decuatroide/FUNBIOB402/Talleres2/Bridgitte Pomachagua/brigitte pomachagua.pdf

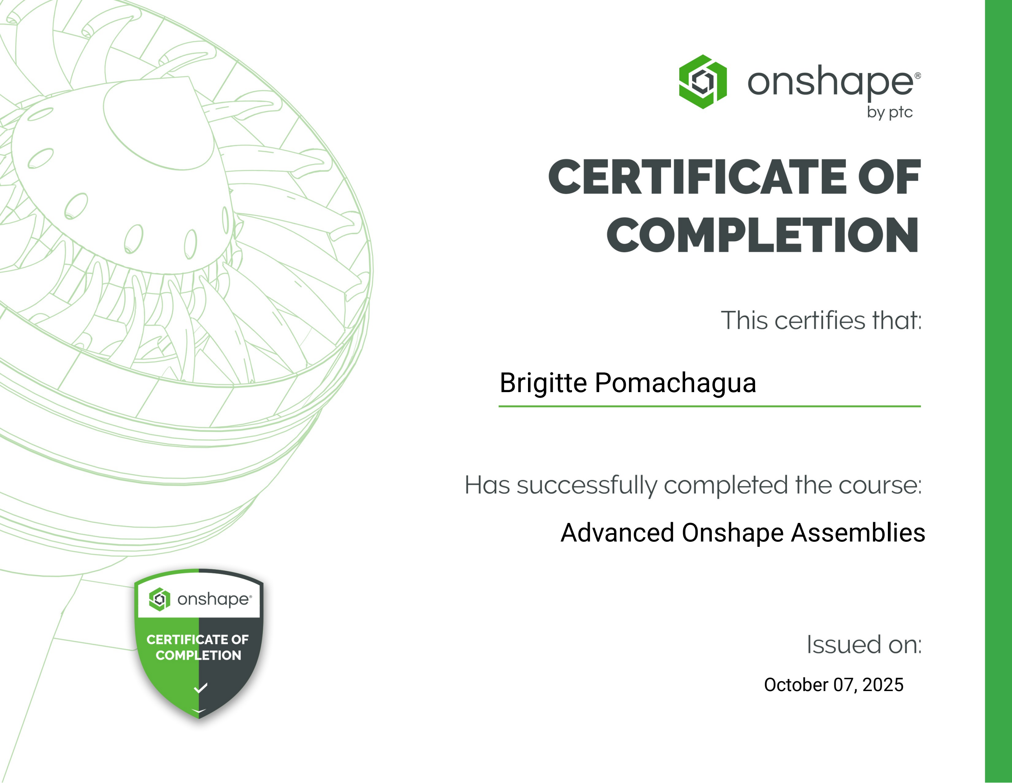
[picture p50: page 1]

Brigitte Pomachagua

Advanced Onshape Assemblies

October 07, 2025
