decuatroide/FUNBIOB402/Talleres2/Leonardo/certificado_taller_elementos_mecánicos Leonardo.pdf

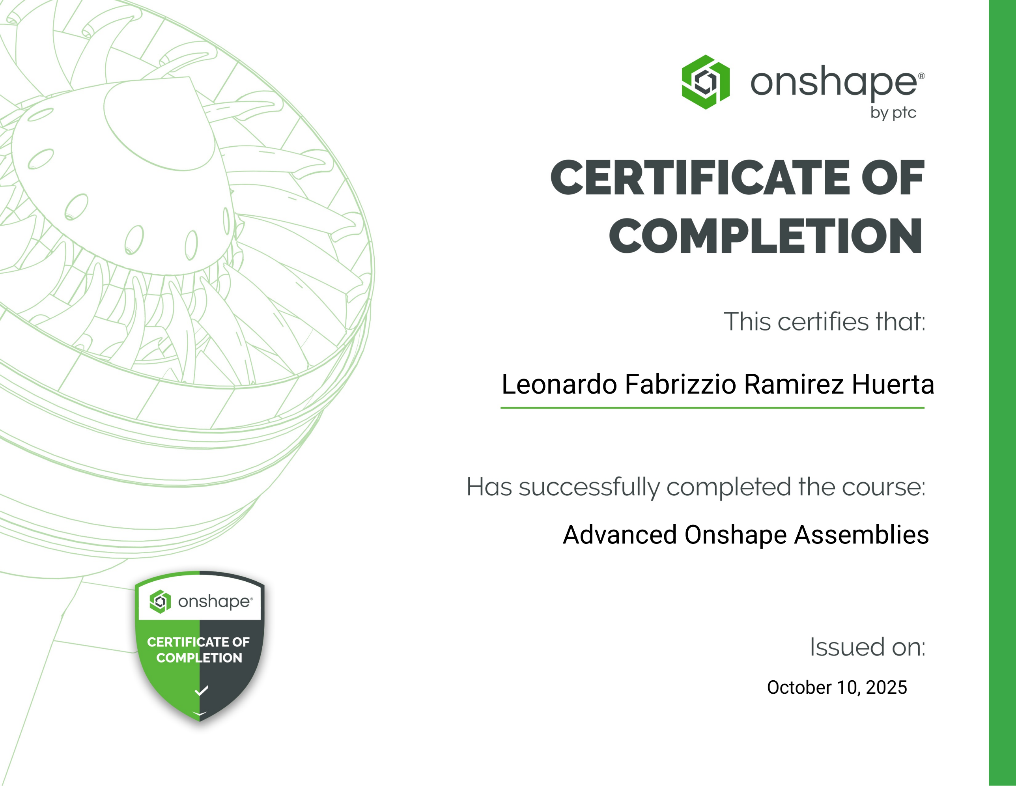
[picture p51: page 1]

Leonardo Fabrizzio Ramirez Huerta

Advanced Onshape Assemblies

October 10, 2025
