decuatroide/FUNBIOB402/Talleres2/Marcela Rojas/certificado taller elementos mecánicos marcela.pdf

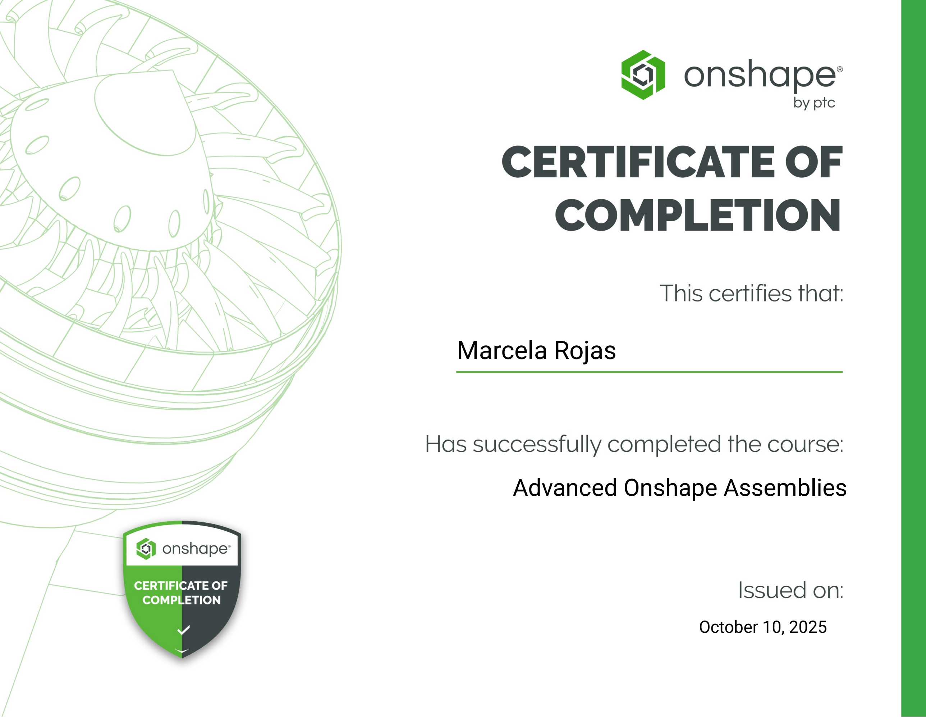
[picture p52: page 1]

Marcela Rojas

Advanced Onshape Assemblies

October 10, 2025
