decuatroide/FUNBIOB402/Talleres2/Oliver/oliver-rimapa-26de84b9-6e77-49f1-8246-cdd332178522-certificate.pdf

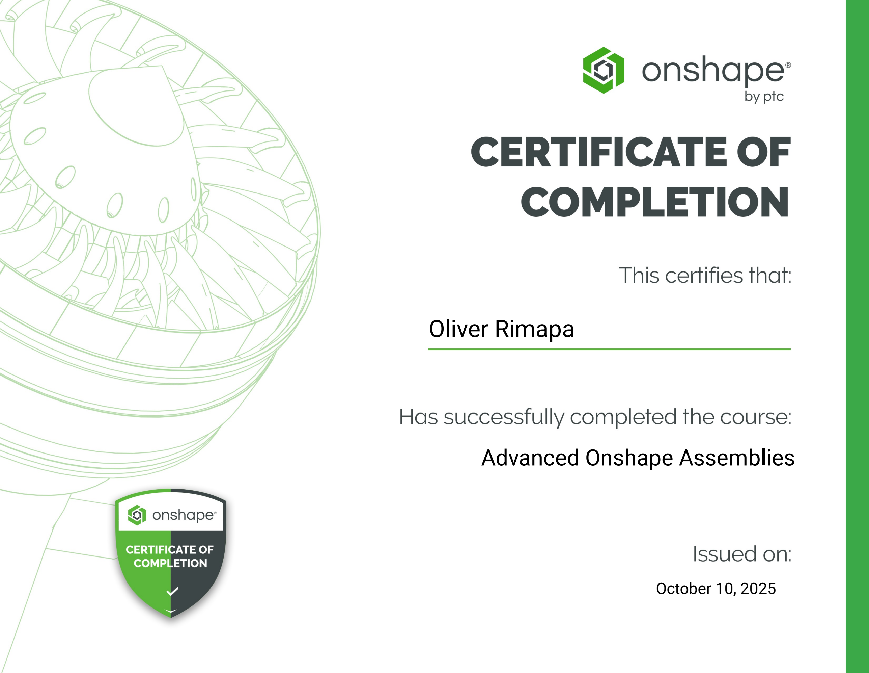
[picture p53: page 1]

Oliver Rimapa

Advanced Onshape Assemblies

October 10, 2025
