decuatroide/FUNBIOB402/Talleres/Briggite/Brigitte Pomachagua.pdf

Brigitte Pomachagua

Introduction to Sketching

September 17, 2025

Brigitte Pomachagua

Introduction to Part Studios

September 19, 2025

Brigitte Pomachagua

September 19, 2025

Multi-Part Part Studios

Brigitte Pomachagua

September 19, 2025

Onshape Assemblies

Brigitte Pomachagua

September 19, 2025

Detailed Drawings
