decuatroide/FUNBIOB402/Talleres/Leonardo/leonardo-fabrizzio-ramirez-huerta-00f52e10-80f0-4916-abce-2b37d8ef5526-certificate.pdf

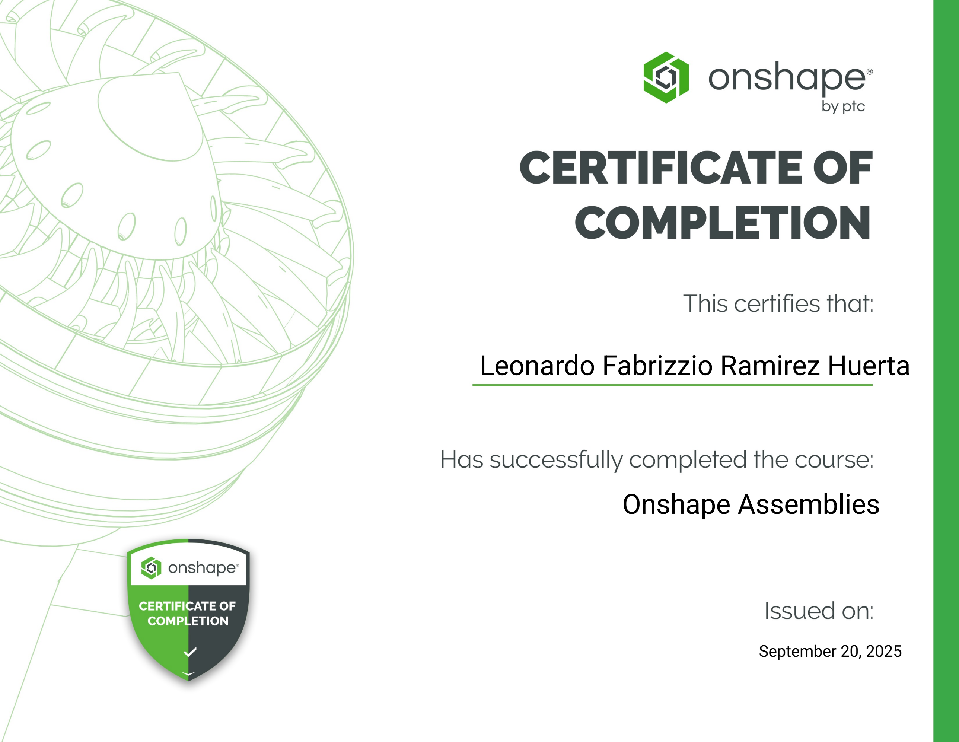
[picture p54: page 1]

Leonardo Fabrizzio Ramirez Huerta

September 20, 2025

Onshape Assemblies
