decuatroide/FUNBIOB402/Talleres/Oliver/oliver-rimapa-e7845775-140b-470d-8c00-d0a61c5a247d-certificate.pdf

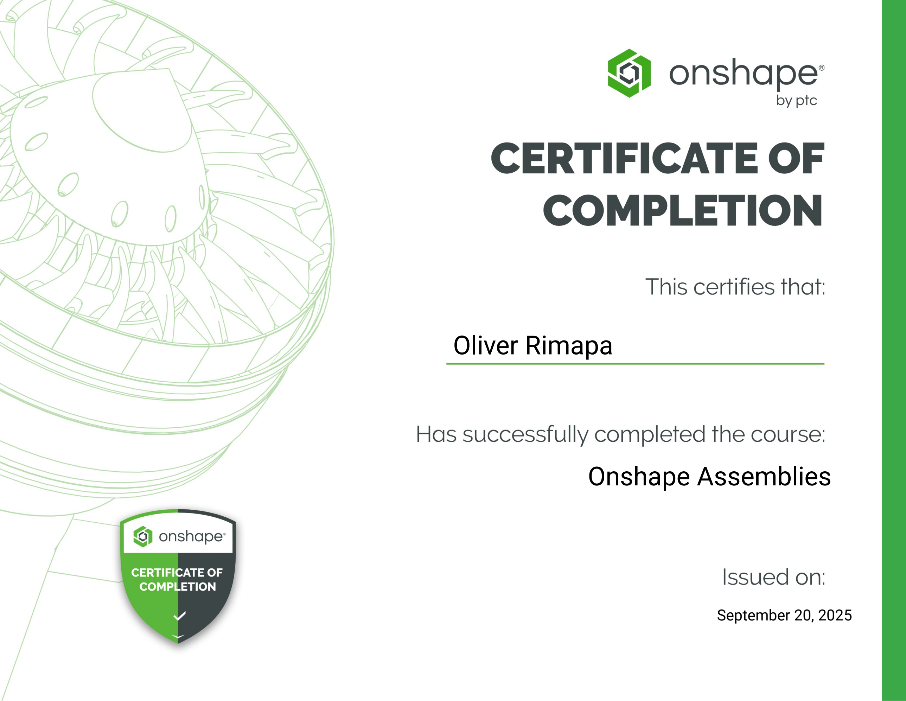
[picture p55: page 1]

Oliver Rimapa

September 20, 2025

Onshape Assemblies
