decuatroide/FUNBIOB402/Talleres/Marcela/certificado 5.pdf

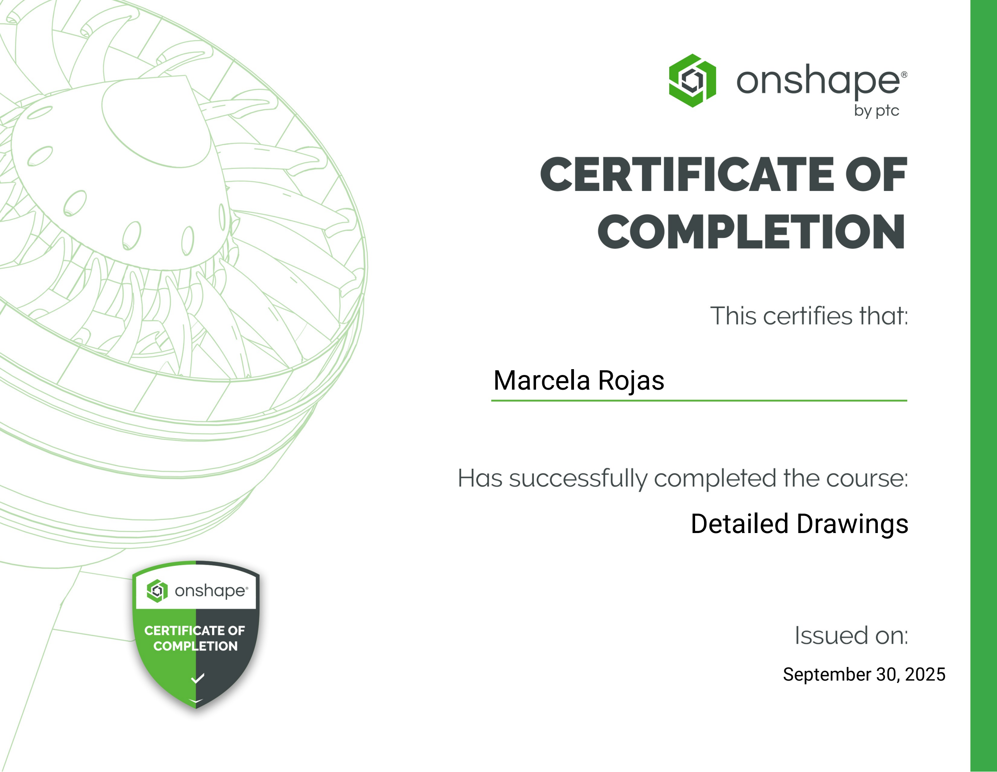
[picture p73: page 1]

Marcela Rojas

September 30, 2025

Detailed Drawings
