decuatroide/FUNBIOB402/Talleres/Marcela/certificado 3.pdf

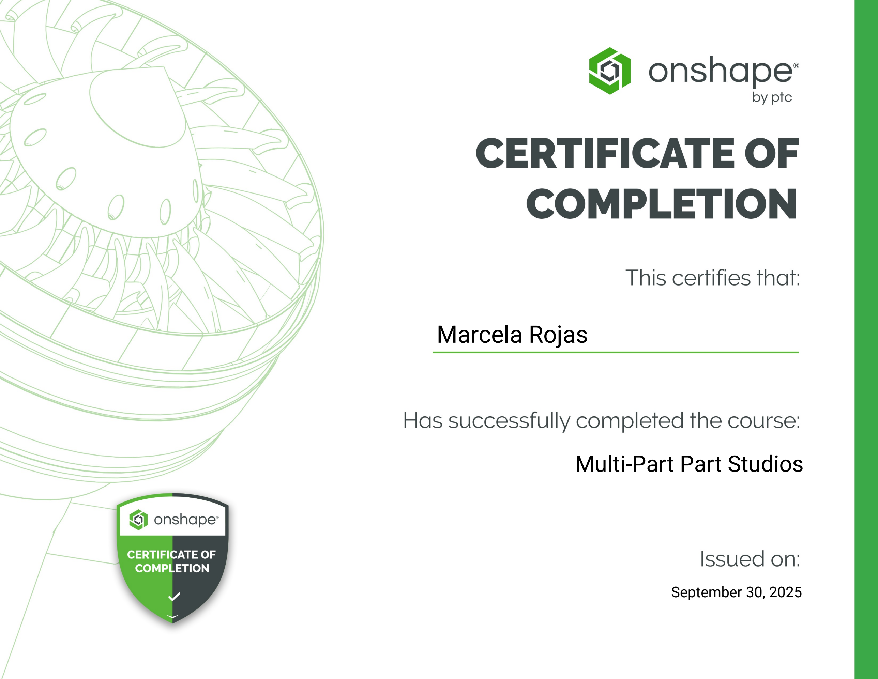
[picture p74: page 1]

Marcela Rojas

September 30, 2025

Multi-Part Part Studios
