decuatroide/FUNBIOB402/Talleres/Marcela/certificado 2.pdf

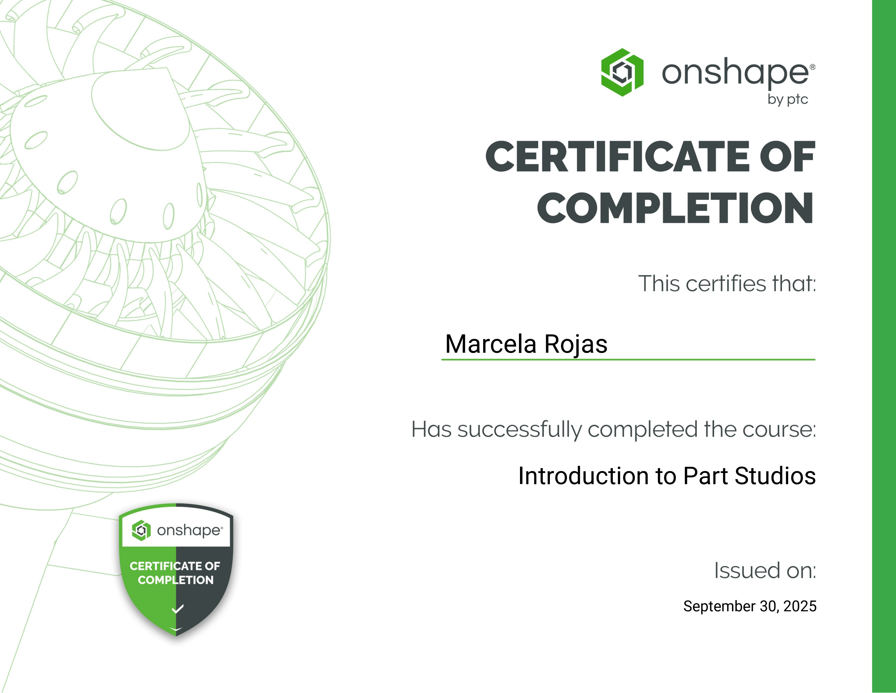
[picture p75: page 1]

Marcela Rojas

Introduction to Part Studios

September 30, 2025
