decuatroide/FUNBIOB402/Talleres/Marcela/certificado 1.pdf

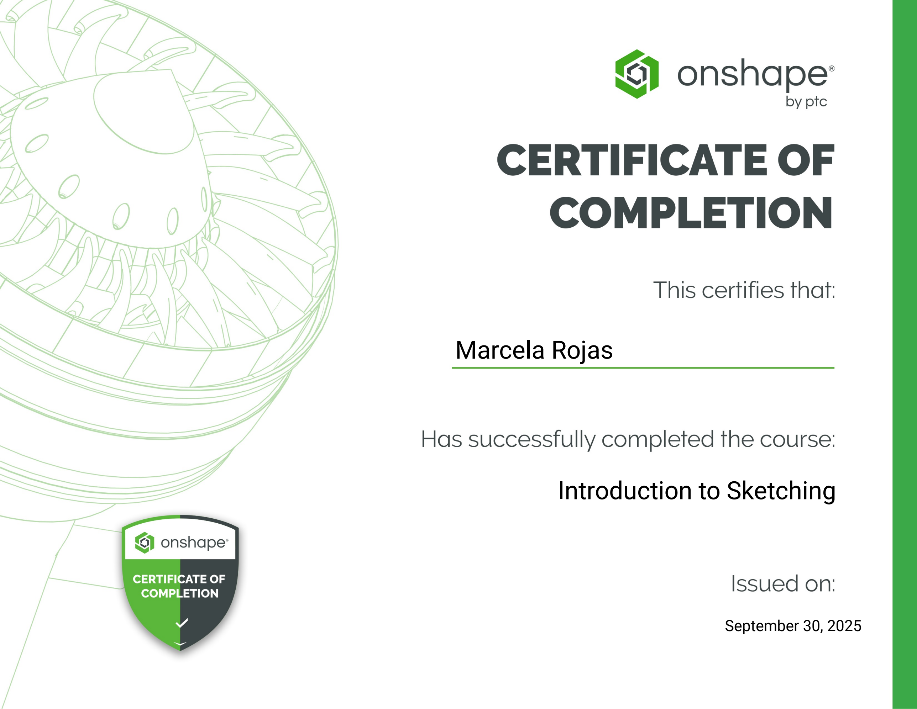
[picture p76: page 1]

Marcela Rojas

Introduction to Sketching

September 30, 2025
