decuatroide/FUNBIOB402/Talleres/Gabriel/Detailed Drawings.pdf

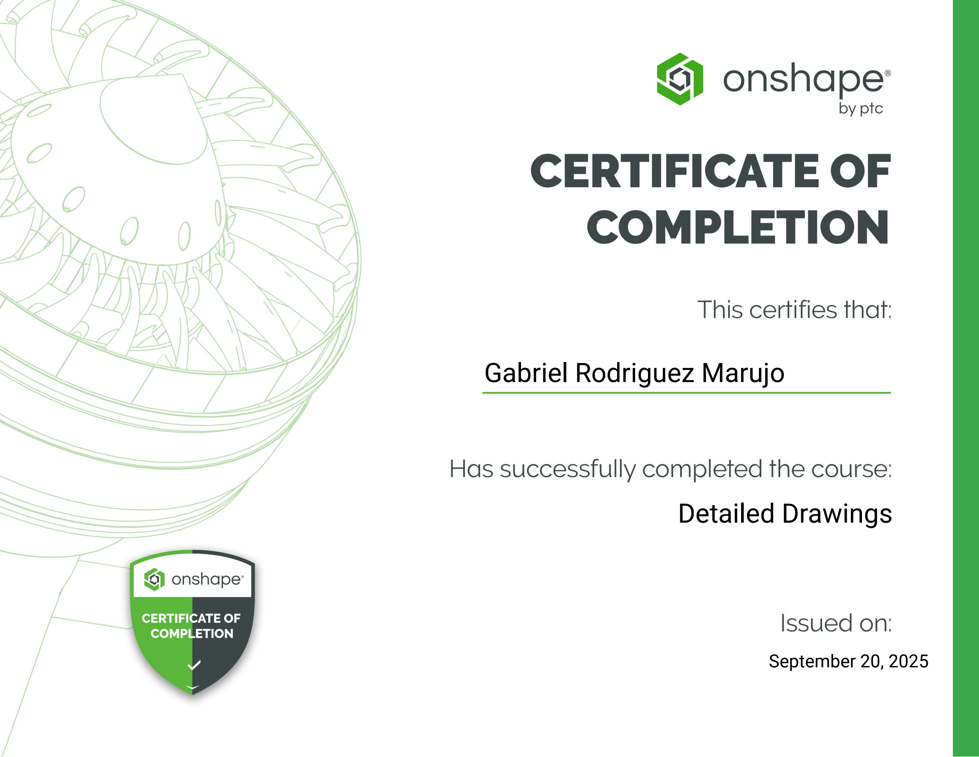
[picture p77: page 1]

Gabriel Rodriguez Marujo

September 20, 2025

Detailed Drawings
