decuatroide/FUNBIOB402/Talleres/Gabriel/Introduction to Part Studios.pdf

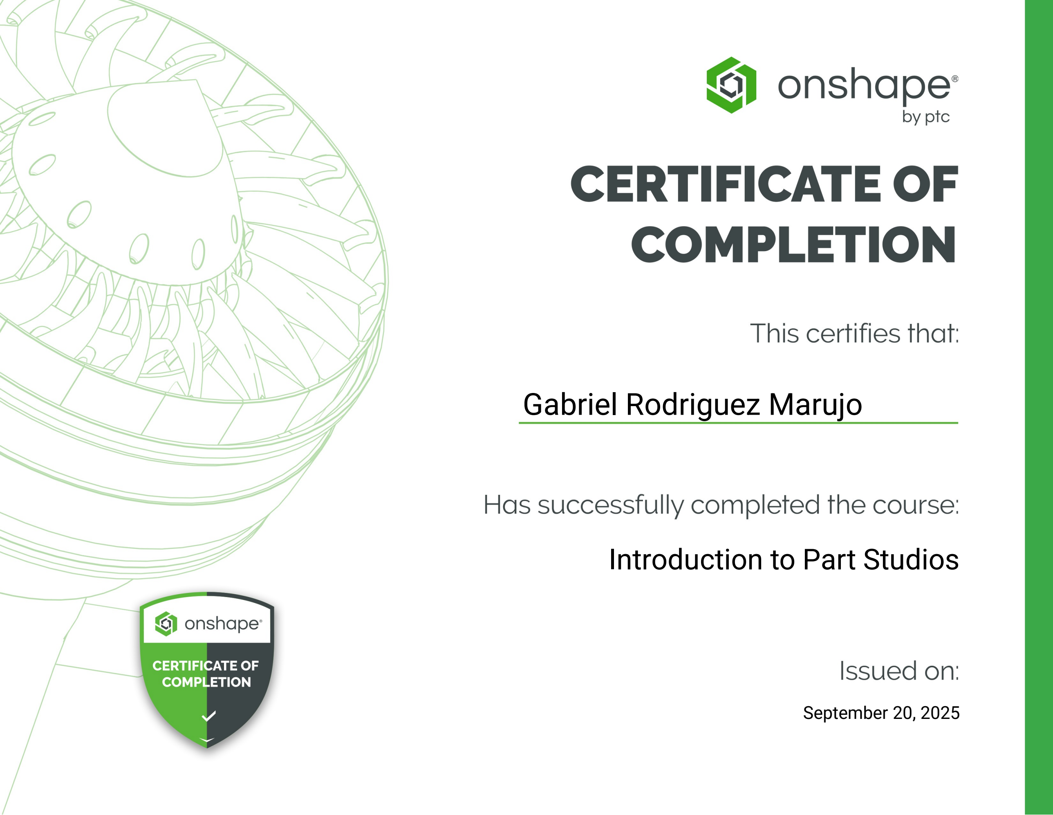
[picture p78: page 1]

Gabriel Rodriguez Marujo

Introduction to Part Studios

September 20, 2025
