decuatroide/FUNBIOB402/Talleres/Gabriel/Introduction to Sketching.pdf

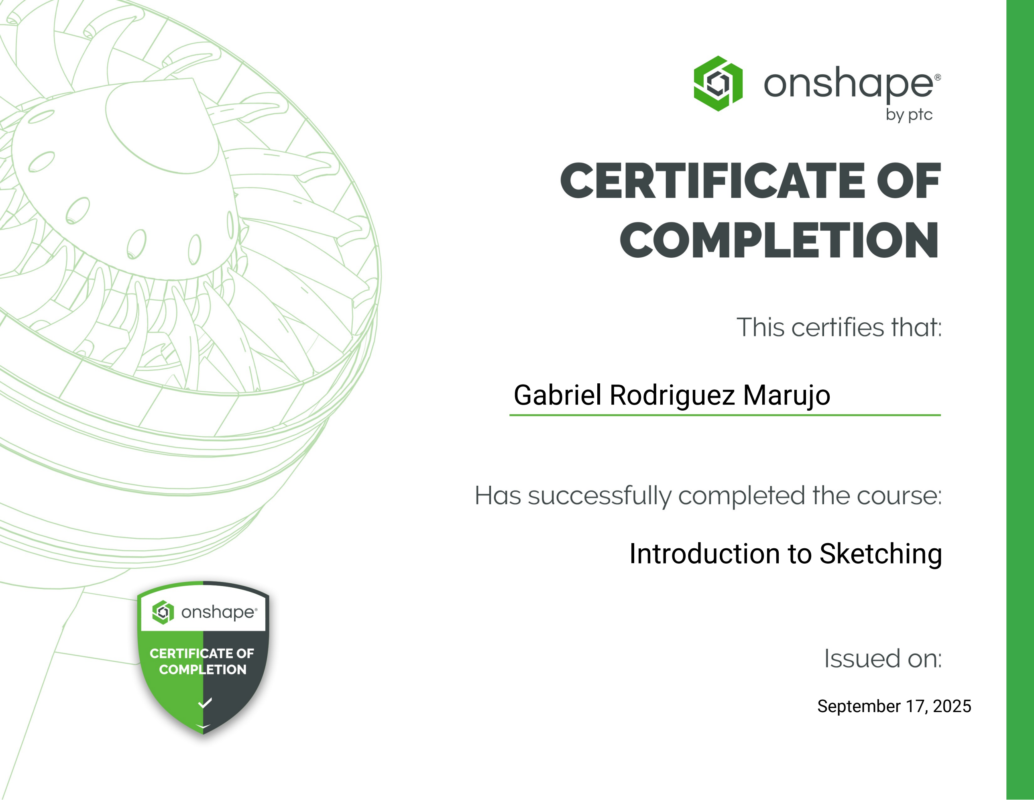
[picture p79: page 1]

Gabriel Rodriguez Marujo

Introduction to Sketching

September 17, 2025
