decuatroide/FUNBIOB402/Talleres/Gabriel/Multi-Part Part Studios.pdf

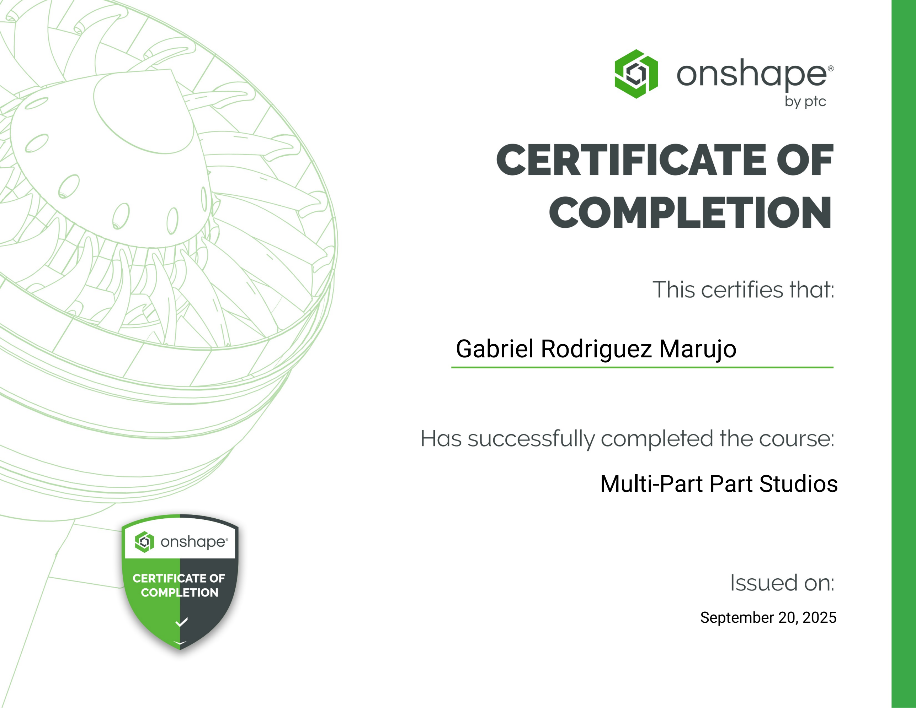
[picture p80: page 1]

Gabriel Rodriguez Marujo

September 20, 2025

Multi-Part Part Studios
