decuatroide/FUNBIOB402/Talleres/Leonardo/leonardo-fabrizzio-ramirez-huerta-042929c8-985e-4253-a575-43340ca856d0-certificate.pdf

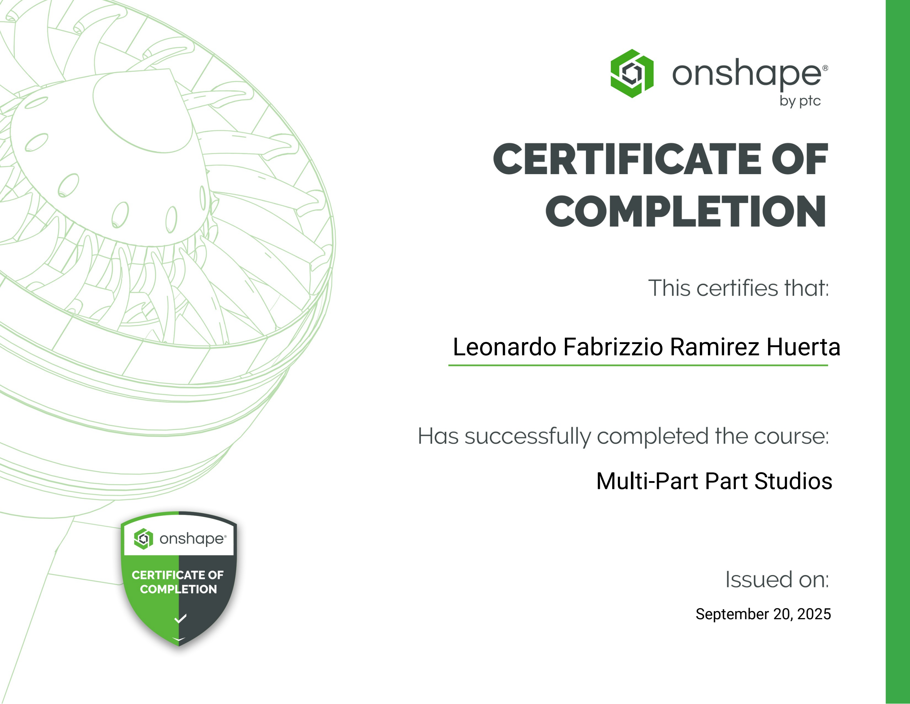
[picture p81: page 1]

Leonardo Fabrizzio Ramirez Huerta

September 20, 2025

Multi-Part Part Studios
