decuatroide/FUNBIOB402/Talleres/Leonardo/leonardo-fabrizzio-ramirez-huerta-1ade5dff-bad6-4393-ad0c-2083a6c78db8-certificate.pdf

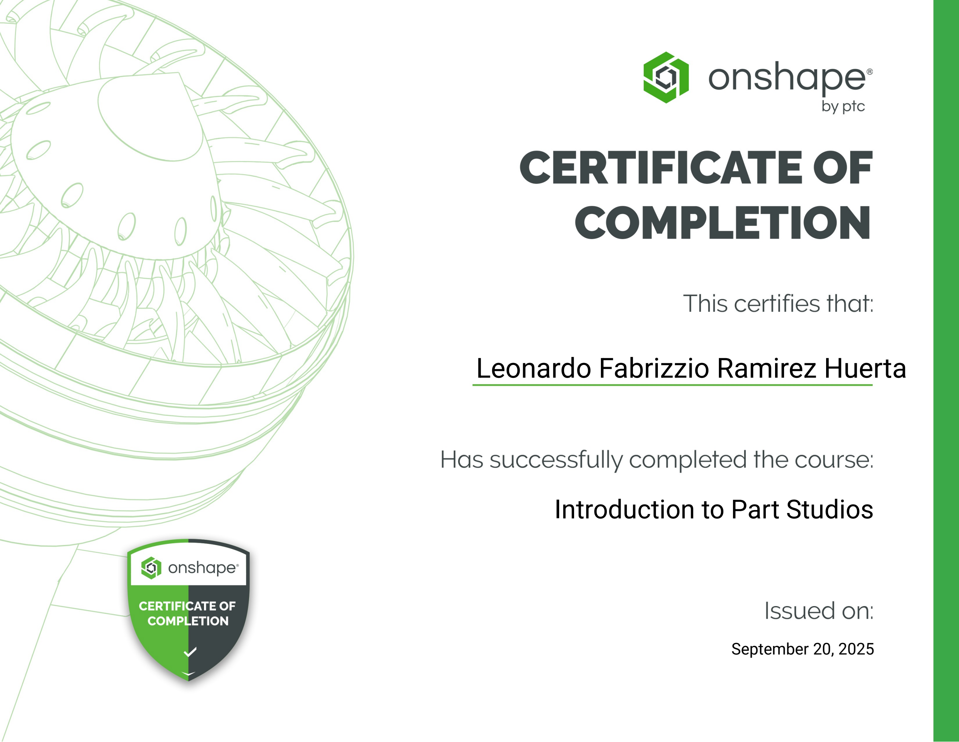
[picture p82: page 1]

Leonardo Fabrizzio Ramirez Huerta

Introduction to Part Studios

September 20, 2025
