decuatroide/FUNBIOB402/Talleres/Leonardo/leonardo-fabrizzio-ramirez-huerta-2d4dcfee-9d83-4cb5-a097-950389071dda-certificate.pdf

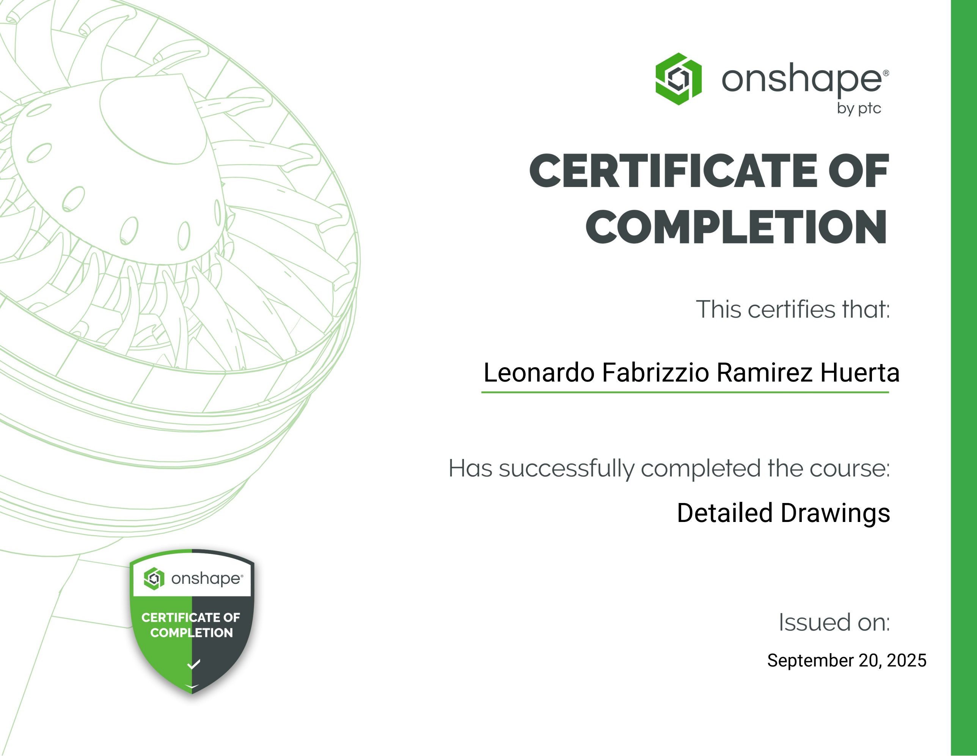
[picture p83: page 1]

Leonardo Fabrizzio Ramirez Huerta

September 20, 2025

Detailed Drawings
