decuatroide/FUNBIOB402/Talleres/Leonardo/leonardo-fabrizzio-ramirez-huerta-379ba665-cea7-4060-8885-238d04ed1d95-certificate.pdf

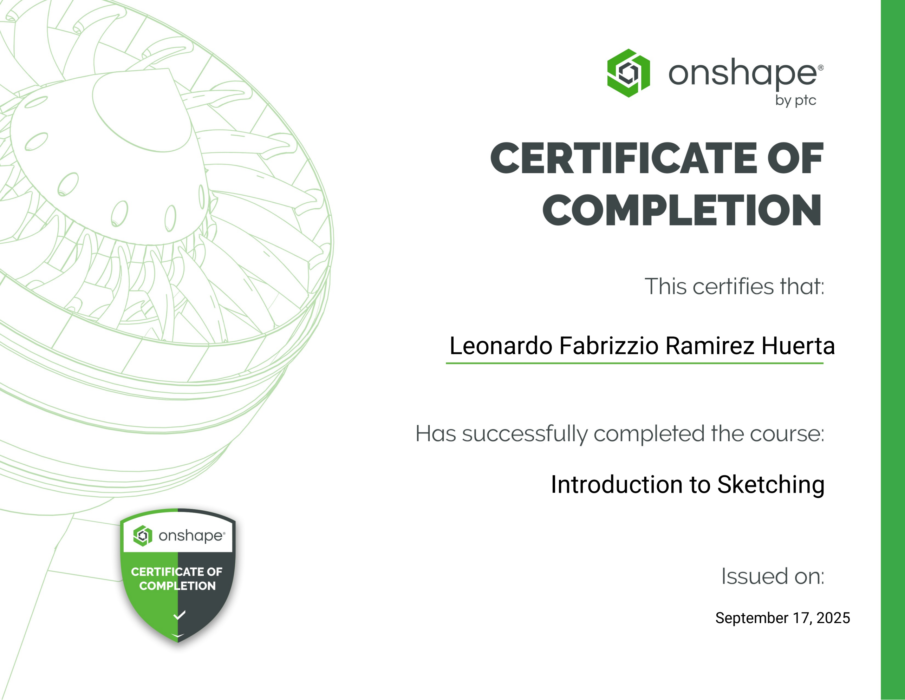
[picture p84: page 1]

Leonardo Fabrizzio Ramirez Huerta

Introduction to Sketching

September 17, 2025
