decuatroide/FUNBIOB402/Talleres/Oliver/oliver-rimapa-0e1e60df-f512-4e64-acf3-dd76d66e0818-certificate.pdf

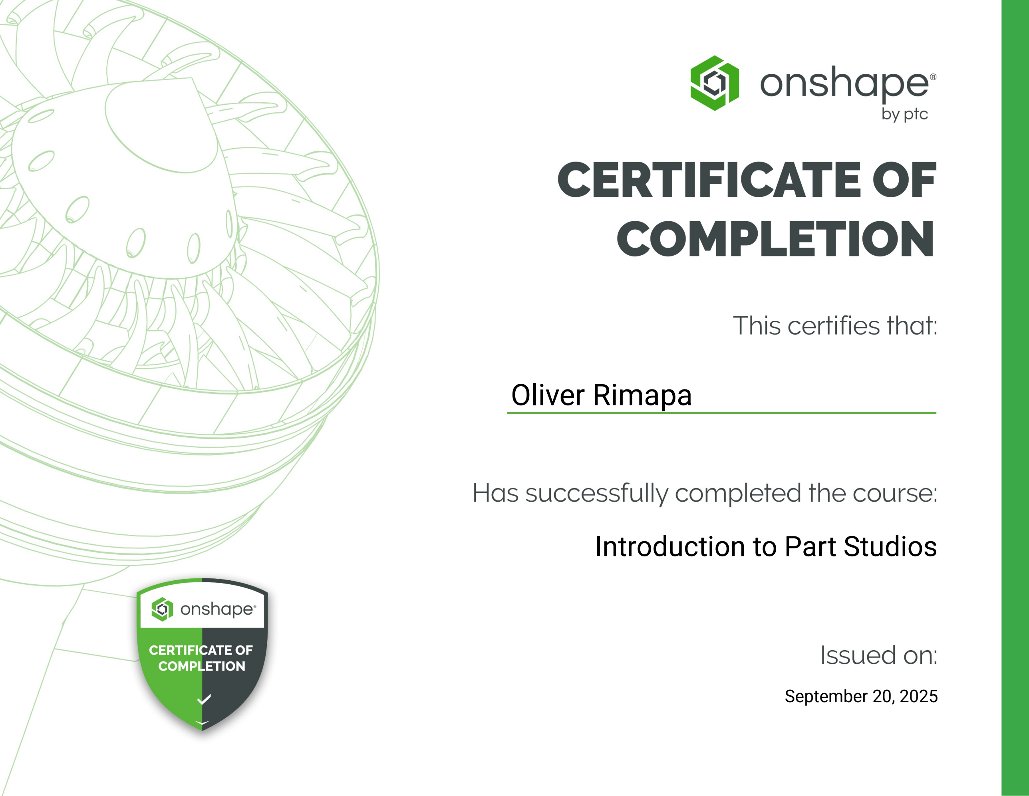
[picture p85: page 1]

Oliver Rimapa

Introduction to Part Studios

September 20, 2025
