decuatroide/FUNBIOB402/Talleres/Oliver/oliver-rimapa-61999745-5ccd-4329-9423-48454300d9ca-certificate.pdf

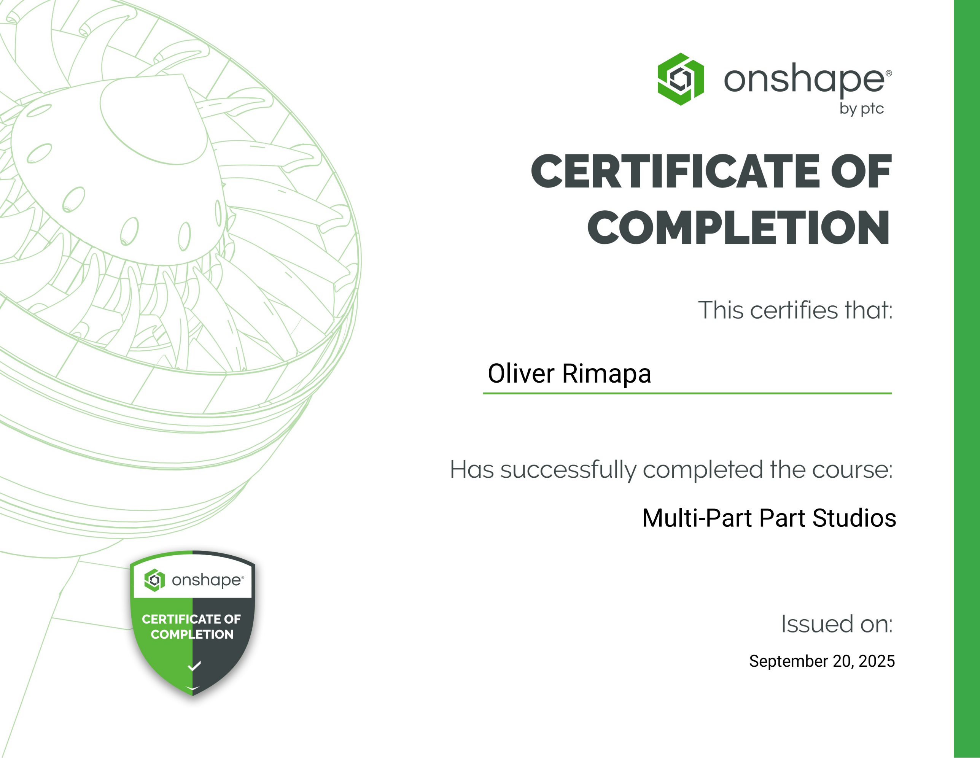
[picture p86: page 1]

Oliver Rimapa

September 20, 2025

Multi-Part Part Studios
