decuatroide/FUNBIOB402/Talleres/Oliver/oliver-rimapa-6b7f9217-4b1c-4249-a582-014349451a3d-certificate.pdf

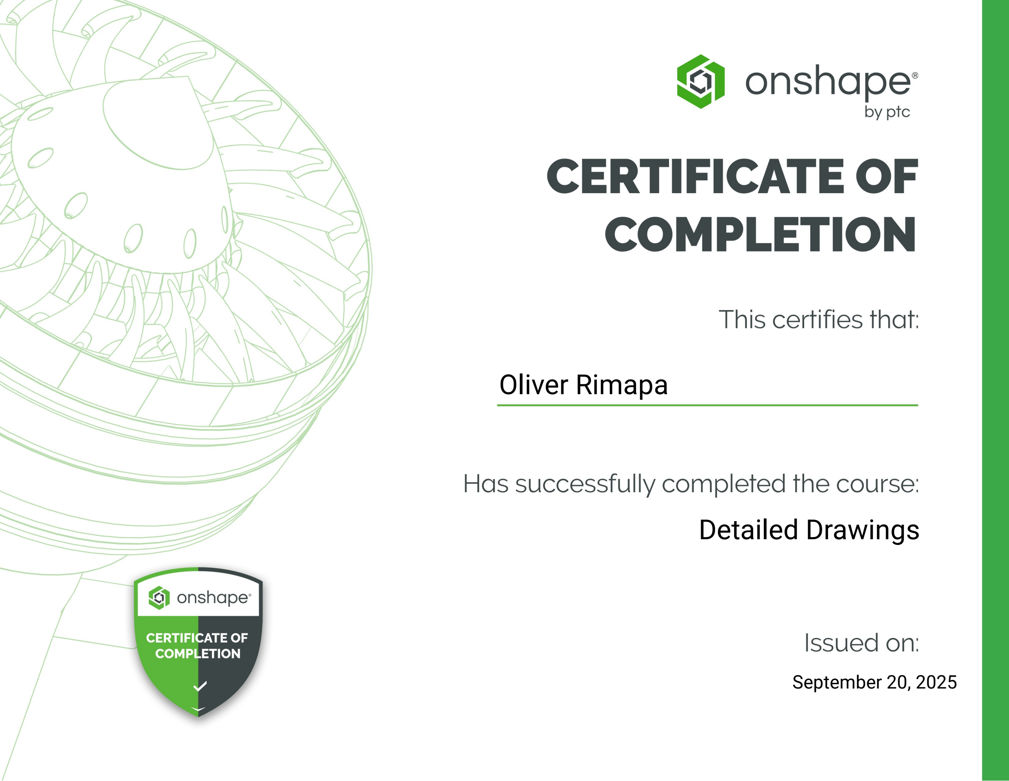
[picture p87: page 1]

Oliver Rimapa

September 20, 2025

Detailed Drawings
