decuatroide/FUNBIOB402/Talleres/Oliver/oliver-rimapa-ac4c721f-f387-4495-b126-dd481988d36d-certificate.pdf

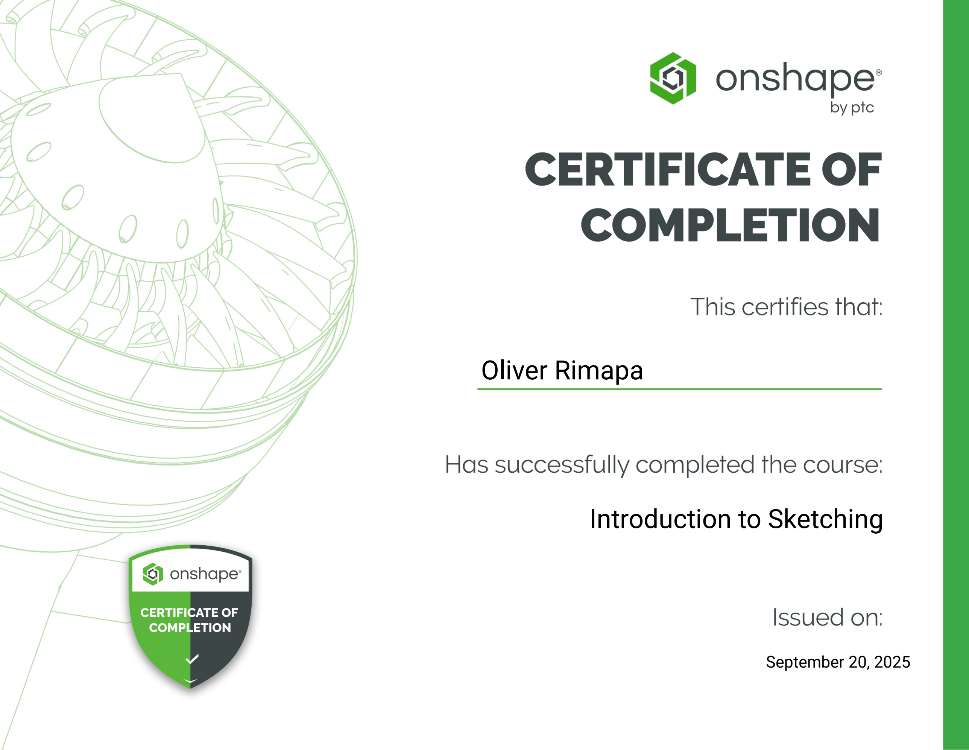
[picture p88: page 1]

Oliver Rimapa

Introduction to Sketching

September 20, 2025
